AtticusO/Hank/mock_servos.py

class servos:
    def __init__(self):
        self.servos = {"waist" : 0, 
                       "shoulder" : 70, 
                       "elbow" : 30}

    def degrees(self):
        self.degrees = 0

    def waist(self):
        degrees = self.servos["waist"]

    def shoulder(self):
        degrees = self.servos["shoulder"]

    def elbow(self):
        degrees = self.servos["elbow"]
