AtticusO/Hank/distance.py

from gpiozero import DistanceSensor


class measure:
    def __init__(self):
        # Define the GPIO pins mapped to Trig and Echo
        self.sensor = DistanceSensor(echo=24, trigger=23)

    def dist(self):
        # gpiozero reports meters, so convert to centimeters
        d = self.sensor.distance * 100
        print(f"Distance: {d:.2f} cm")
        return d

if __name__ == "__main__":
    m = measure()
    while True:
        d = m.dist()
